Daan080/FlowGuard/ARDUINO/Opkomende_technologieën/presentatie  opkomende technologieën.pptx

## OPKOMENDE TECHNOLOGIeËN HYBRID PROTOTYPING

Afbeelding met overdekt, ontwerp Door AI gegenereerde inhoud is mogelijk onjuist.

- Jasper Dekeyser & Daan Dobbelaere

## OPDRACHT

- GGO - FlowGuard
- Timer instellen, starten en stoppen
- Werkstatus delen (groen/rood)
- Tijd + werkstatus tonen gebruiker
- Werkstatus tonen omgeving

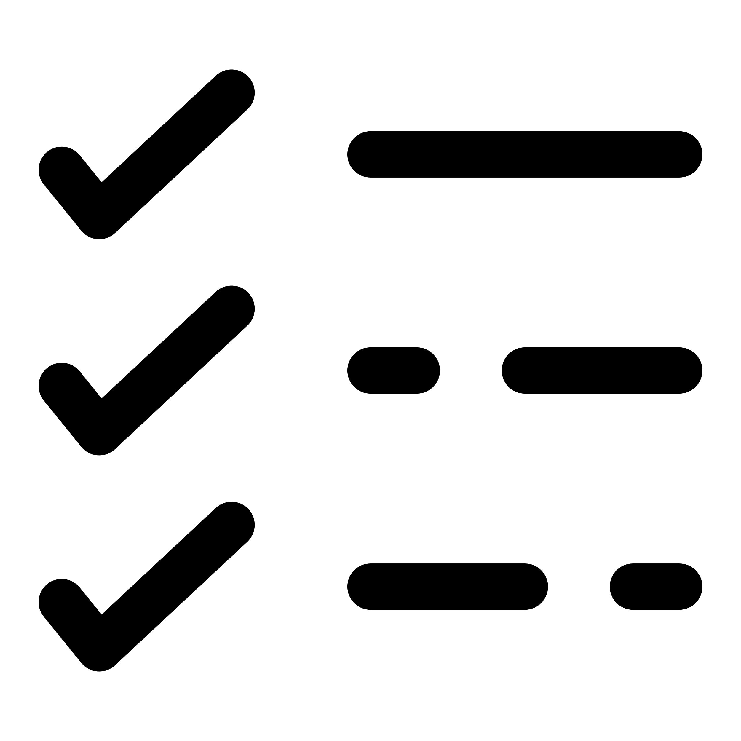
[picture p28: figure]

## MATERIAAL

- Arduino Nano
- RGB LCD-scherm
- Rotary Encoder
- LED Arcade drukknoppen
- Adafruit NeoPixel RGB-ledring

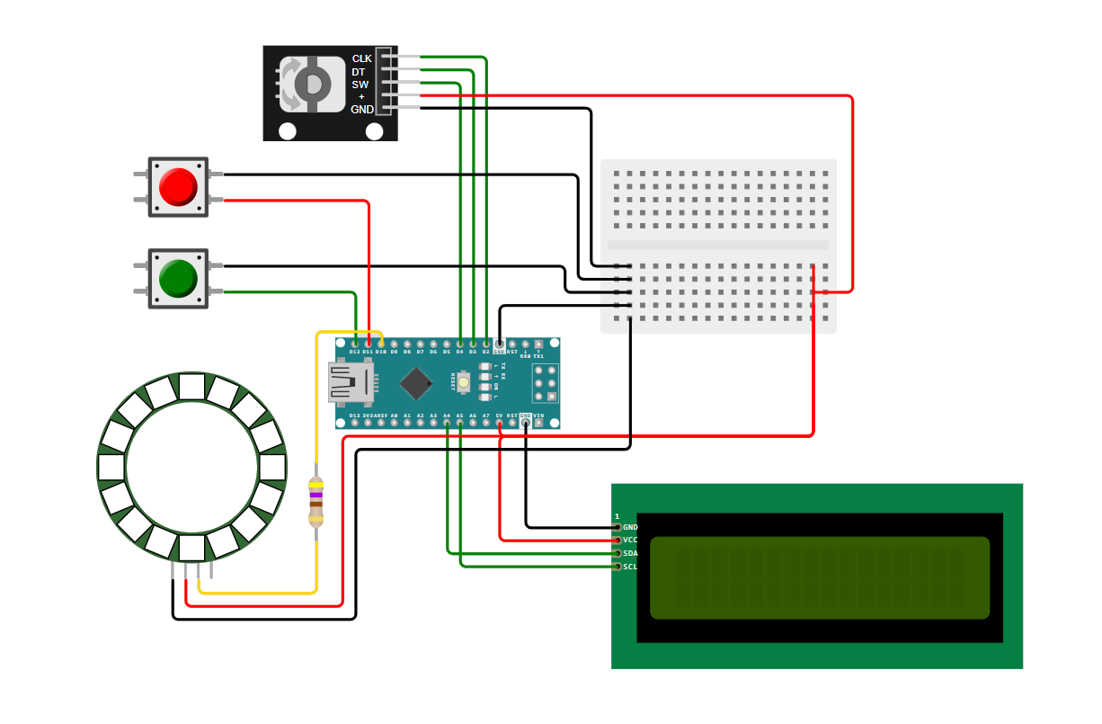
[picture p29: figure]
Afbeelding met tekst, schermopname, diagram, cirkel Door AI gegenereerde inhoud is mogelijk onjuist.
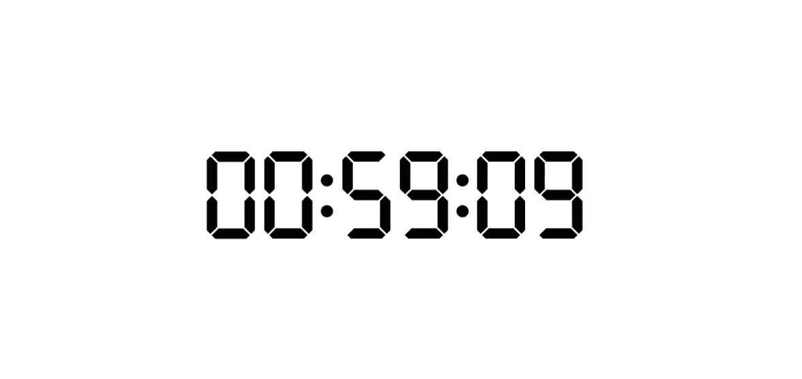
[picture p30: figure]

## MOEILIJKHEDEN

CODE:
  - Gevoeligheid van rotary encoder
  - Alle functies samenvoegen
HARDWARE:
  - Slechte/fragiele contacten
  - Alles compact en geordend houden

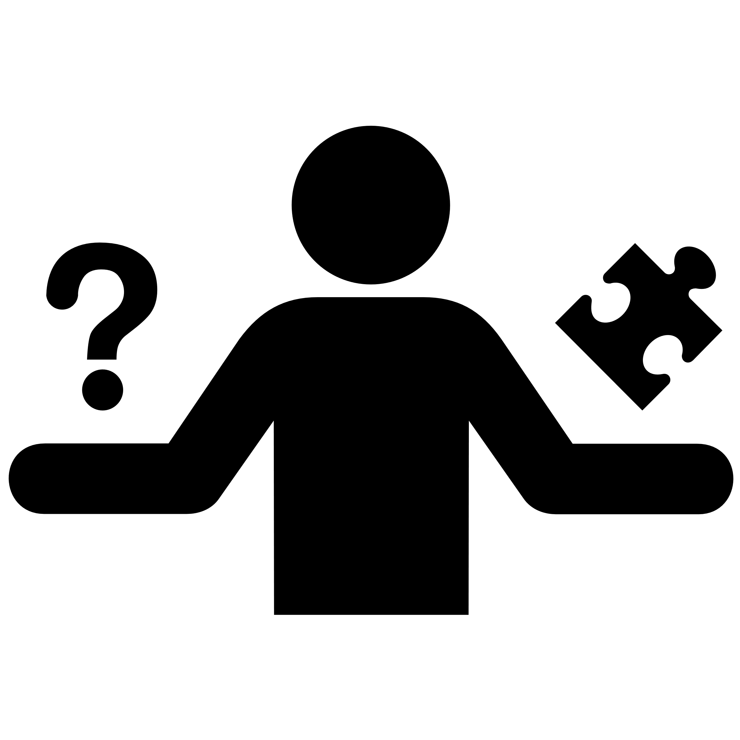
[picture p31: figure]

## DEMONSTRATIE

## TOEKOMST

Bluetooth verbinding
Connectie met laptop (Protopie)
Draadloos opladen

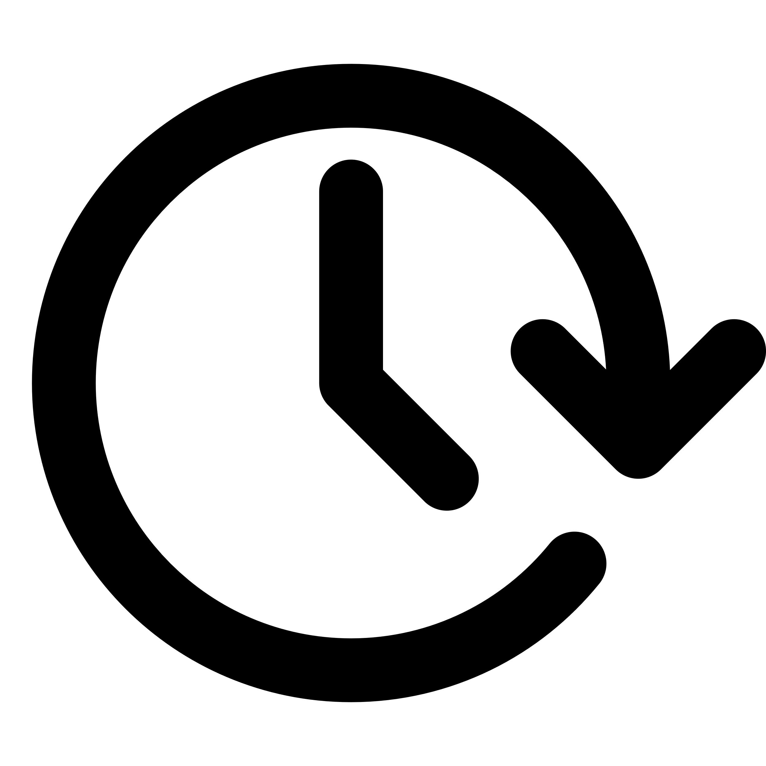
[picture p32: figure]
