Daan080/FlowGuard/protocols/Discover_innovatrix-FlowGuard.docx

| | COLLEGA’S | WERKGEVER | OPDRACHTGEVER
Current state | Custumor segment | Gestrest, overwerkt, niet genoeg vrije tijd | Deadlines te halen, moet team tevreden houden | Verwacht goed werk, stelt deadlines
| Key trends | Groeiende aantal burn-outs Maatschappelijke druk | Groeiende aantal burn-outs Aandacht mentaal welzijn | Snelle resultaten, verslaan concurentie
| need | Werk haalbaar maken, beweging | Sneller werk, contente werknemers | Snel, efficiënt resultaat
| Current alternatives | Praten , staandesk | HR, persoonlijke initiatieven | Computers, grote bedrijven
Future state | Value promise | Minder stress, betere communicatie, efficiëntie | Betere communicatie, beter overzicht | Sneller, beter resultaat

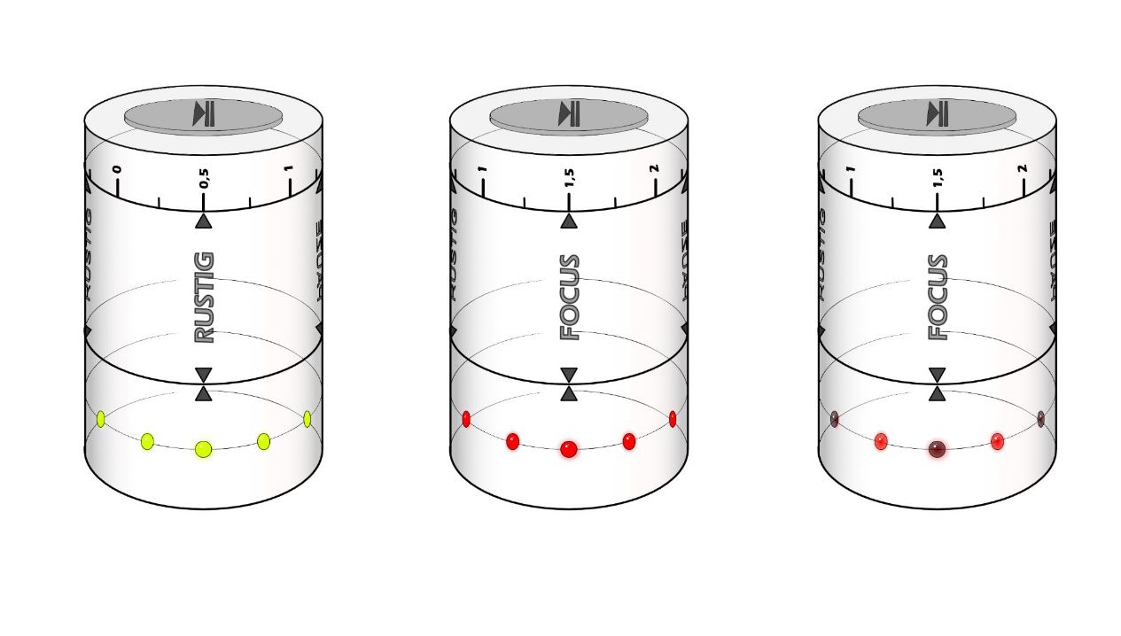
[picture p47: figure]

| Solution
| Barriers | Prijs, privacy, collega’s weten niet hoe het werkt | Prijs
