Daan080/FlowGuard/img/methodologie_oud.png

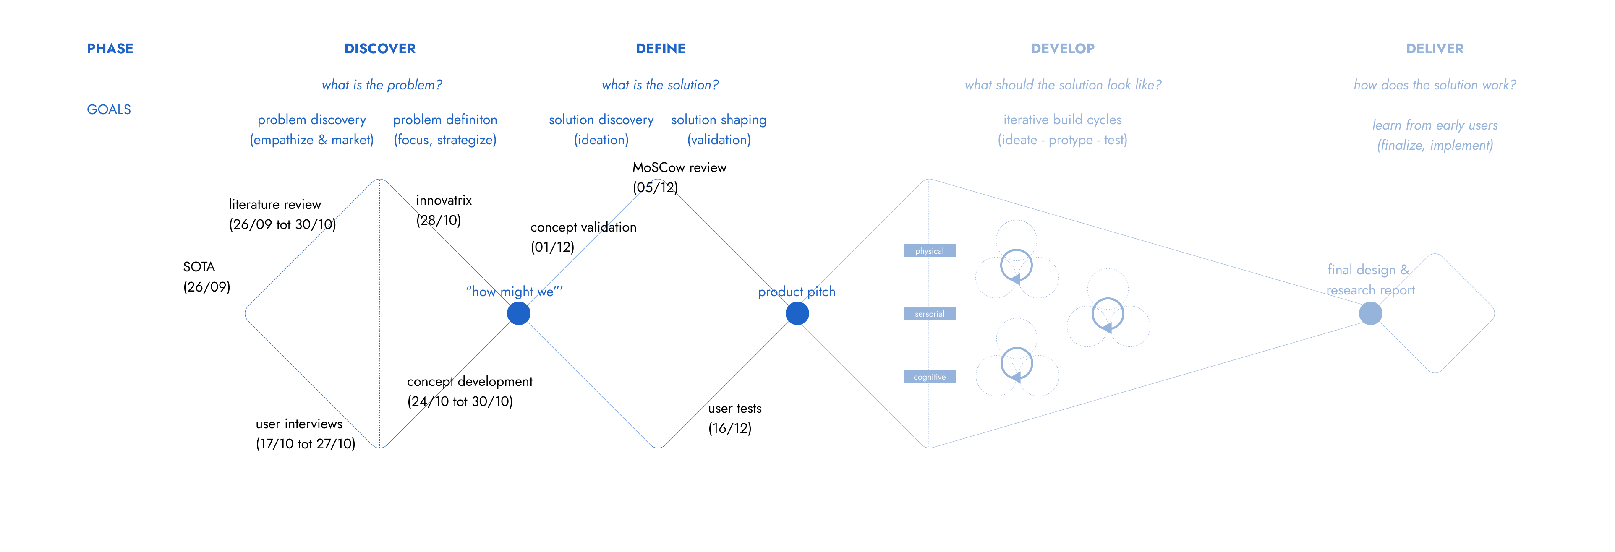
img/methodologie_oud.png
