Daan080/FlowGuard/Renders/render_1.png

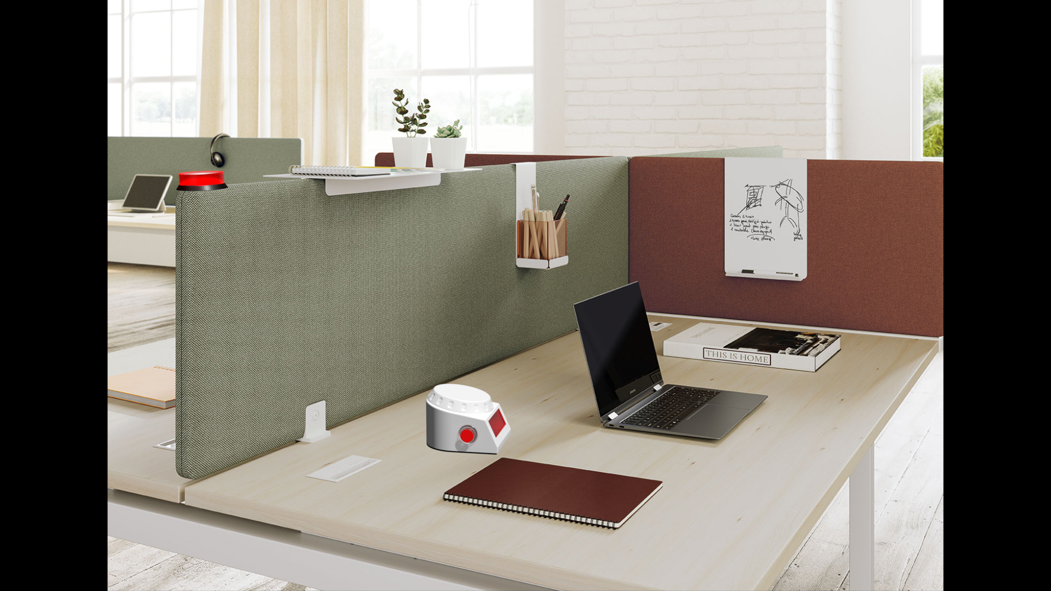
Renders/render_1.png
