Daan080/FlowGuard/Renders/render_2.png

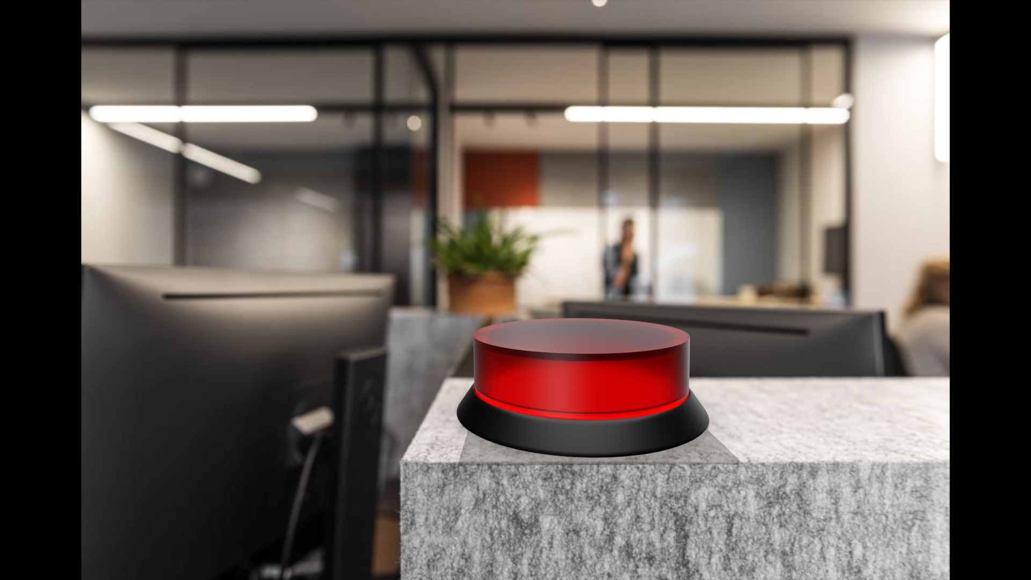
Renders/render_2.png
