Daan080/FlowGuard/Renders/render_3.png

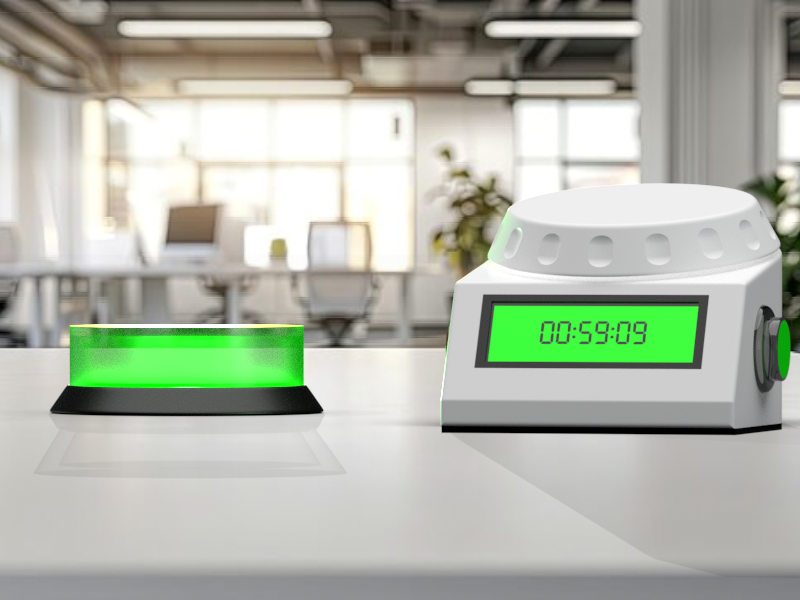
Renders/render_3.png
