Daan080/FlowGuard/Renders/render_4.png

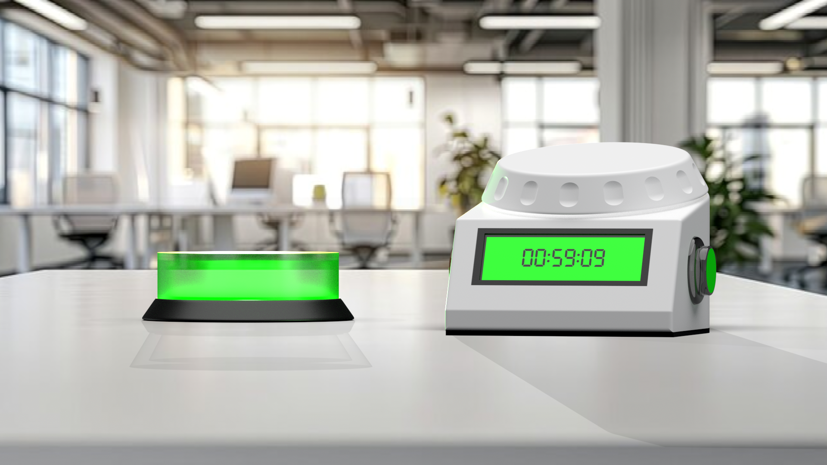
Renders/render_4.png
